e3w2q/Kasumigasane-keypad/doc/all_switch_attach.jpg

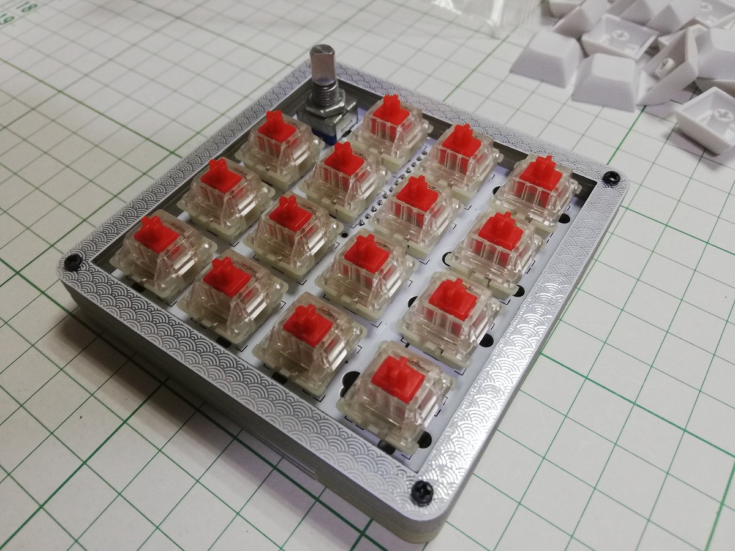
doc/all_switch_attach.jpg
