e3w2q/Kasumigasane-keypad/doc/frame.jpg

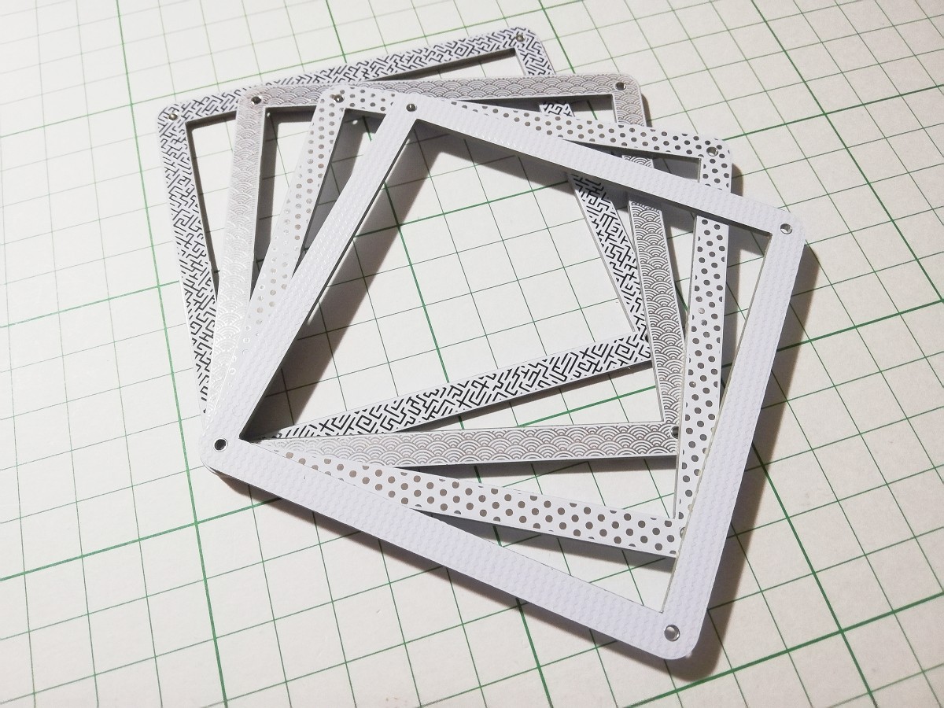
doc/frame.jpg
