e3w2q/Kasumigasane-keypad/doc/Kasumigasane.jpg

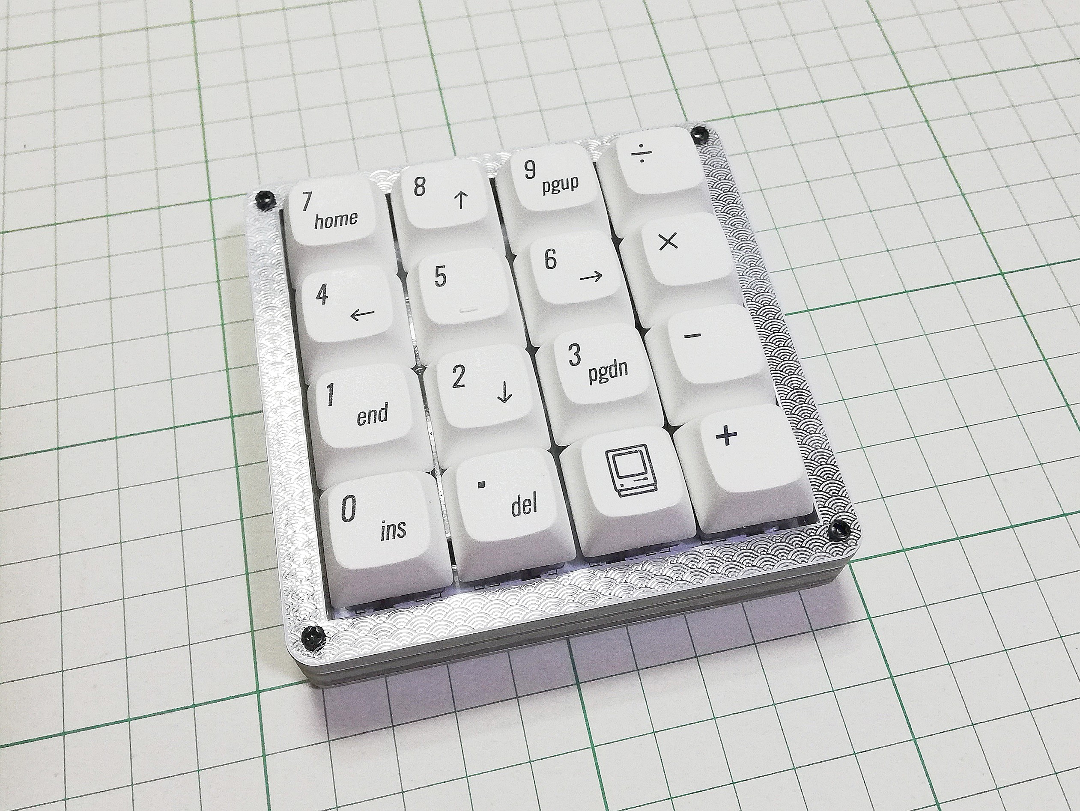
doc/Kasumigasane.jpg
