e3w2q/Kasumigasane-keypad/doc/layer_pin.jpg

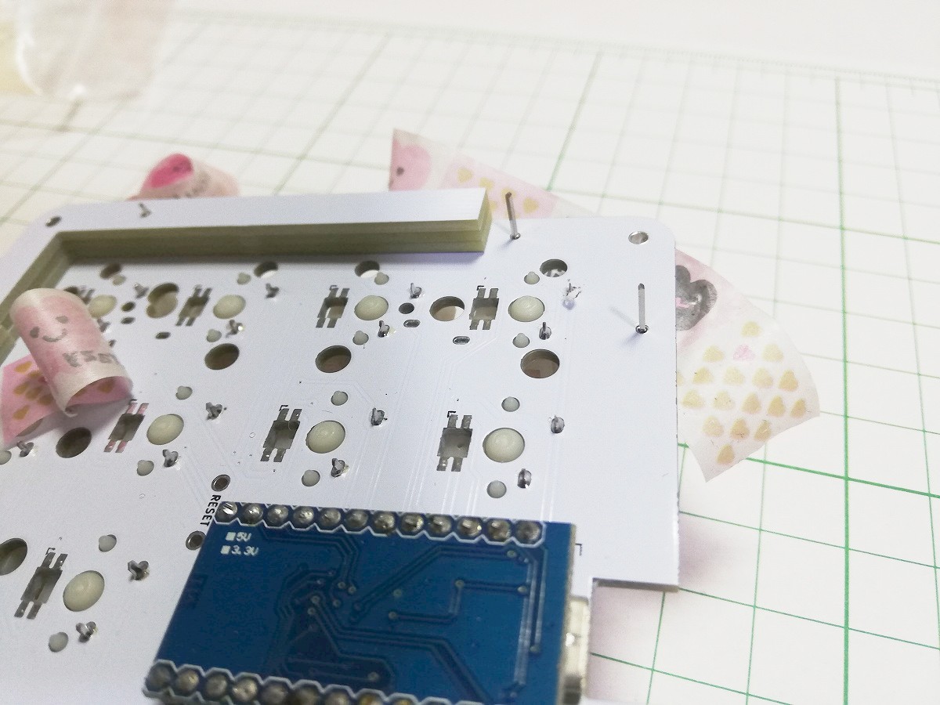
doc/layer_pin.jpg
