e3w2q/Kasumigasane-keypad/doc/rotaryencoder_attach.jpg

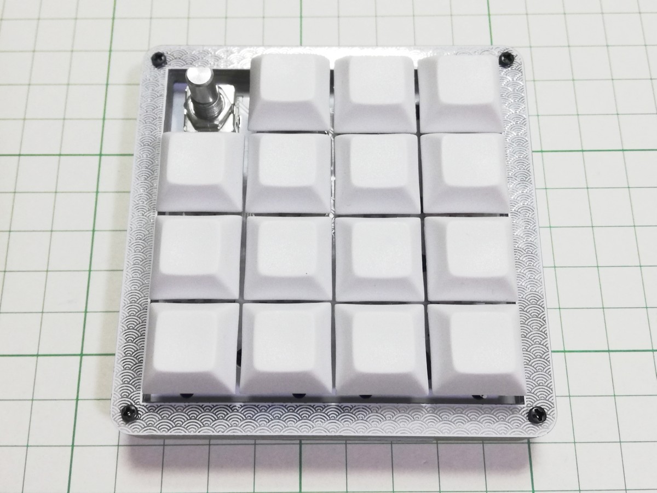
doc/rotaryencoder_attach.jpg
