e3w2q/Kasumigasane-keypad/doc/side_maskingtape2.jpg

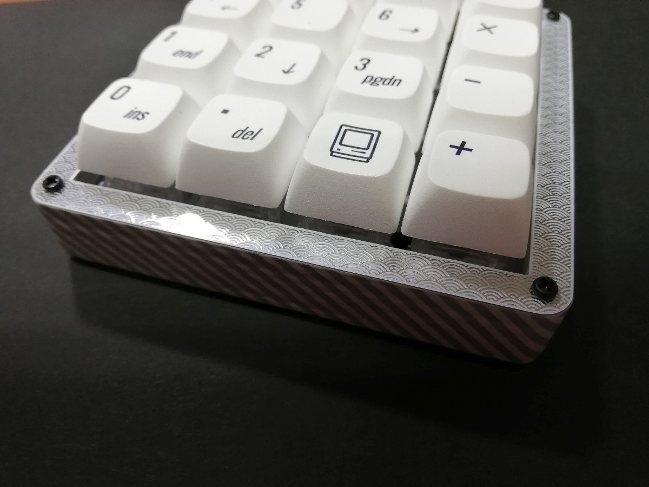
doc/side_maskingtape2.jpg
